benjaminwand/3d-printed-labial-pipe/0.17.2.FCStd

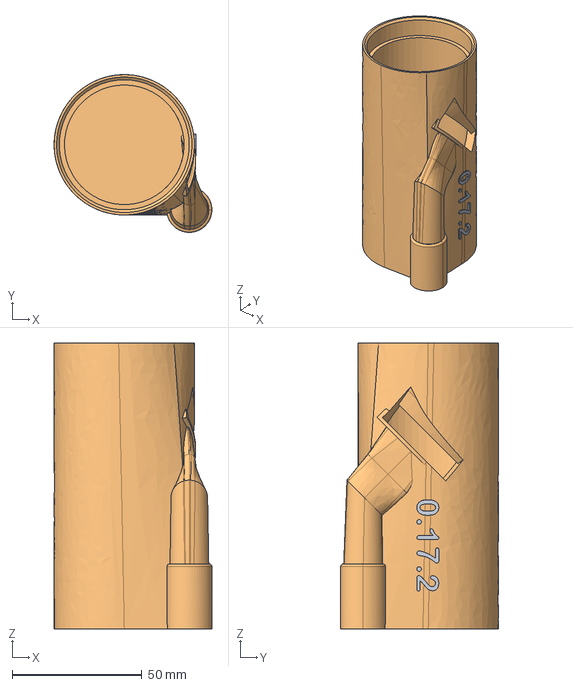
[picture p43: CAD file, 2018-04-24]
0.17.2.FCStd
60.7 x 60.7 x 110.0 mm
version number
Cut whole thing
