benjaminwand/3d-printed-labial-pipe/flue and labium only/sad+bent.FCStd

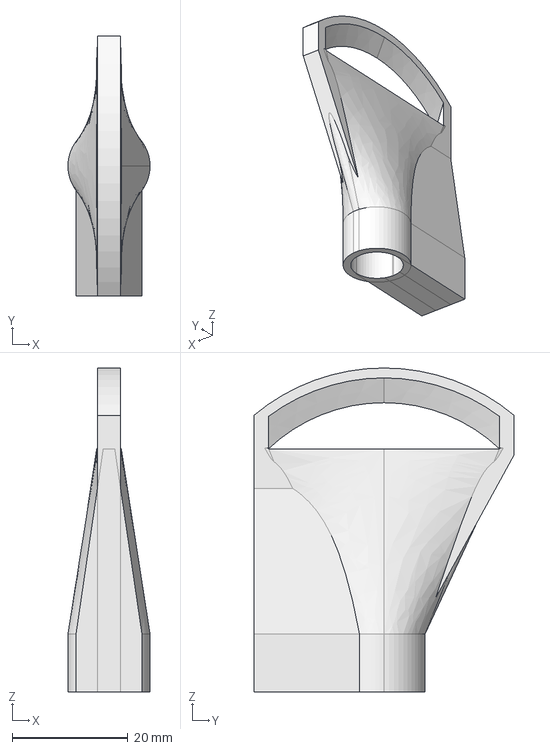
[picture p44: CAD file, 2018-07-03]
flue and labium only/sad+bent.FCStd
14.2 x 45.0 x 56.0 mm
