benjaminwand/3d-printed-labial-pipe/tuning and misc/8 tuning sliders.FCStd

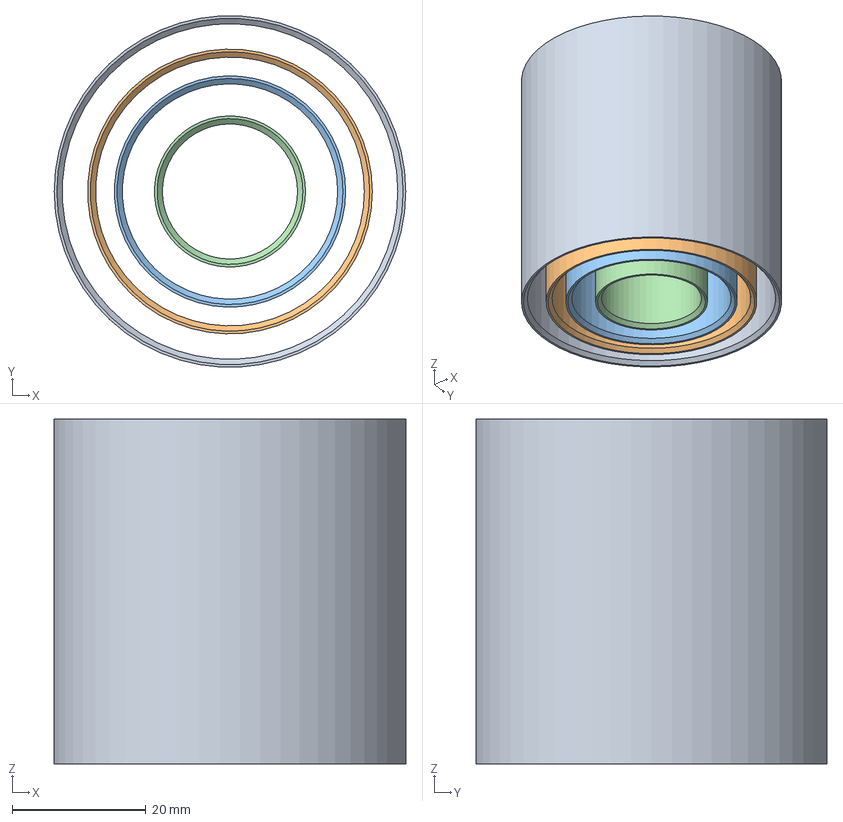
[picture p45: CAD file, 2018-03-27]
tuning and misc/8 tuning sliders.FCStd
52.6 x 52.5 x 51.6 mm
