benjaminwand/3d-printed-labial-pipe/0.15.9.FCStd

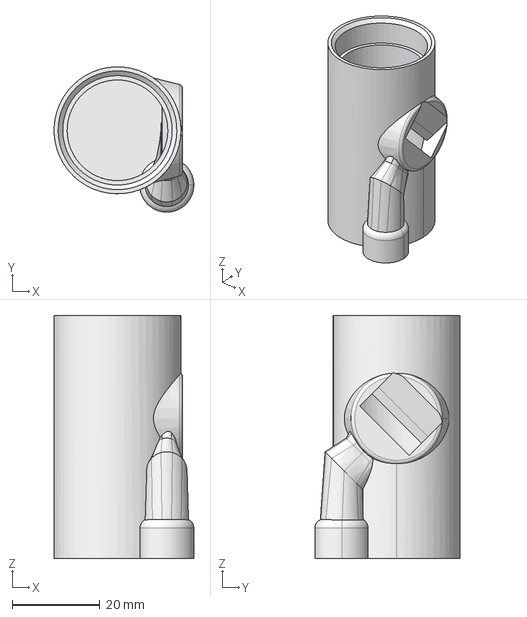
[picture p46: CAD file, 2018-04-24]
0.15.9.FCStd
31.9 x 33.2 x 55.5 mm
