benjaminwand/3d-printed-labial-pipe/flue and labium only/straight2.FCStd

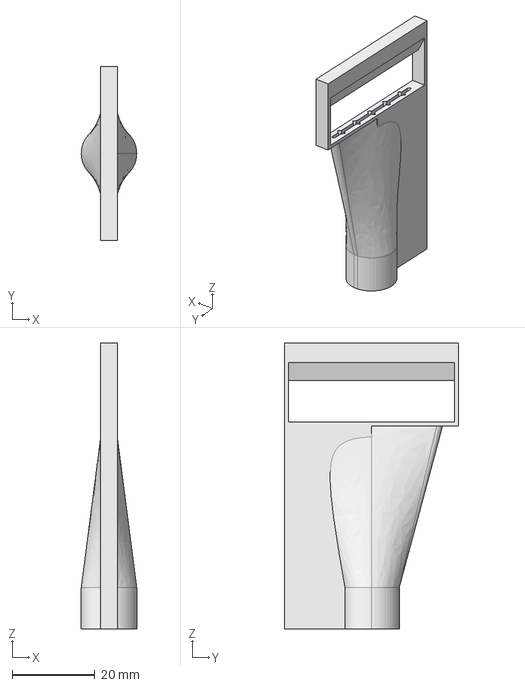
[picture p47: CAD file, 2018-05-06]
flue and labium only/straight2.FCStd
13.4 x 42.0 x 69.0 mm
