benjaminwand/3d-printed-labial-pipe/0.17.1.FCStd

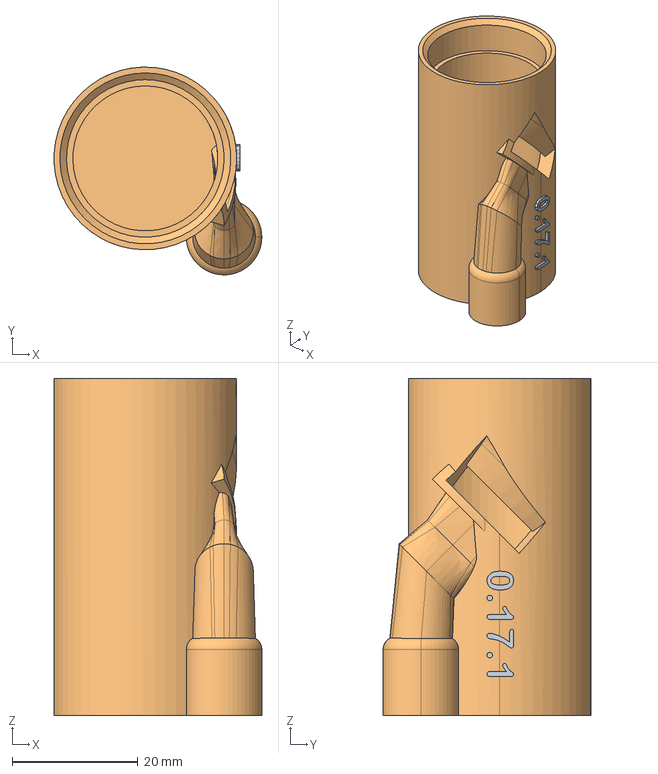
[picture p48: CAD file, 2018-04-16]
0.17.1.FCStd
33.0 x 33.0 x 53.5 mm
version number
Cut whole thing
