benjaminwand/3d-printed-labial-pipe/flue and labium only/curved-3.FCStd

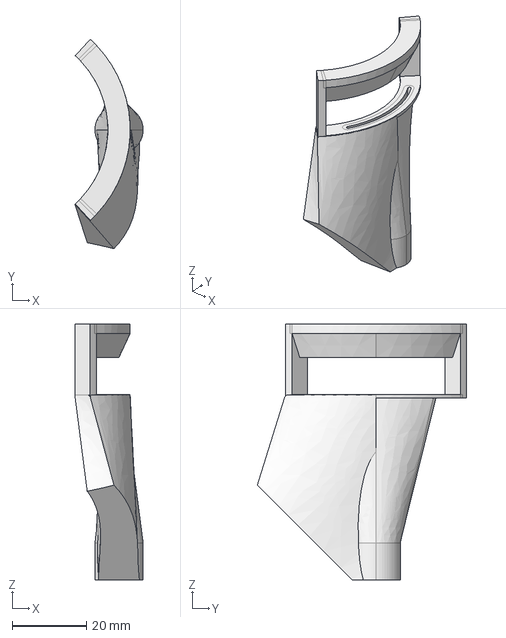
[picture p49: CAD file, 2018-04-24]
flue and labium only/curved-3.FCStd
18.4 x 56.4 x 69.0 mm
