benjaminwand/3d-printed-labial-pipe/0.17.FCStd

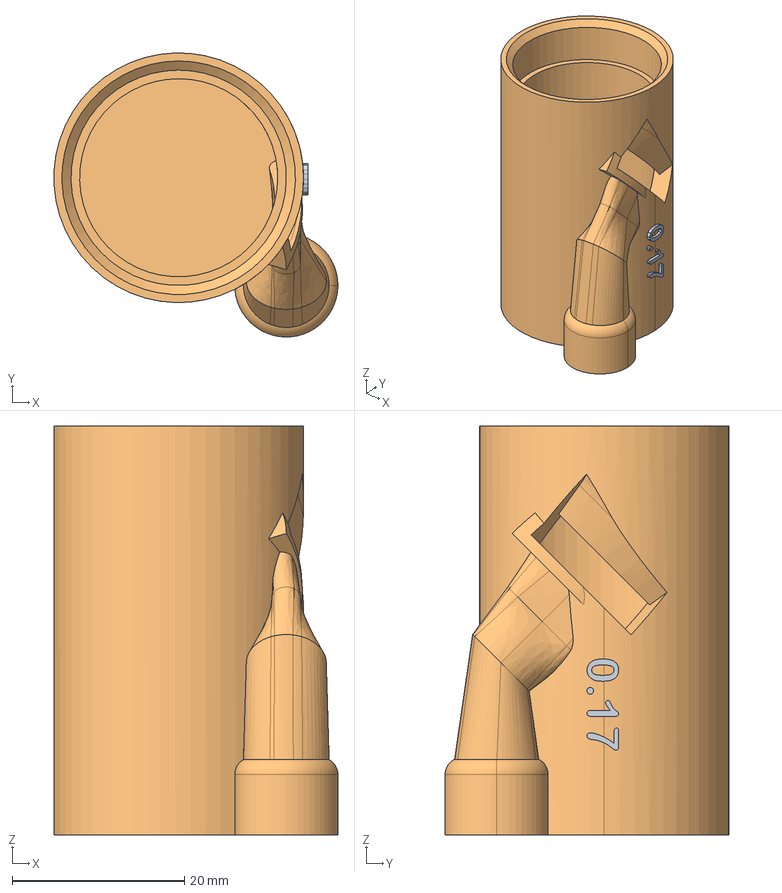
[picture p50: CAD file, 2018-04-16]
0.17.FCStd
33.0 x 33.0 x 47.5 mm
version number
Cut whole thing
