benjaminwand/3d-printed-labial-pipe/flue and labium only/curved-2.FCStd

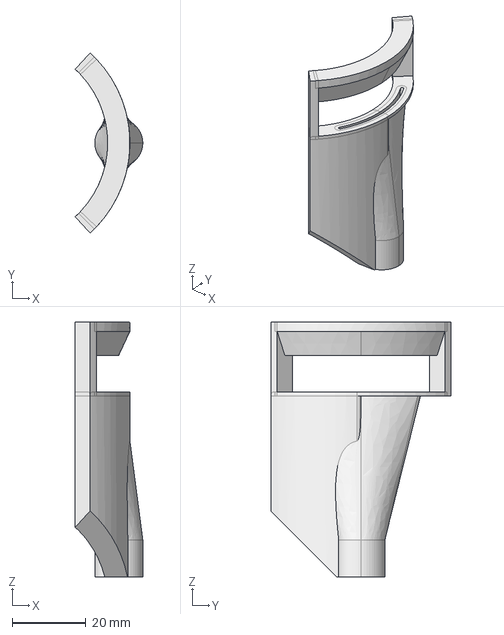
[picture p51: CAD file, 2018-04-24]
flue and labium only/curved-2.FCStd
18.3 x 48.8 x 69.0 mm
