benjaminwand/3d-printed-labial-pipe/0.08.FCStd

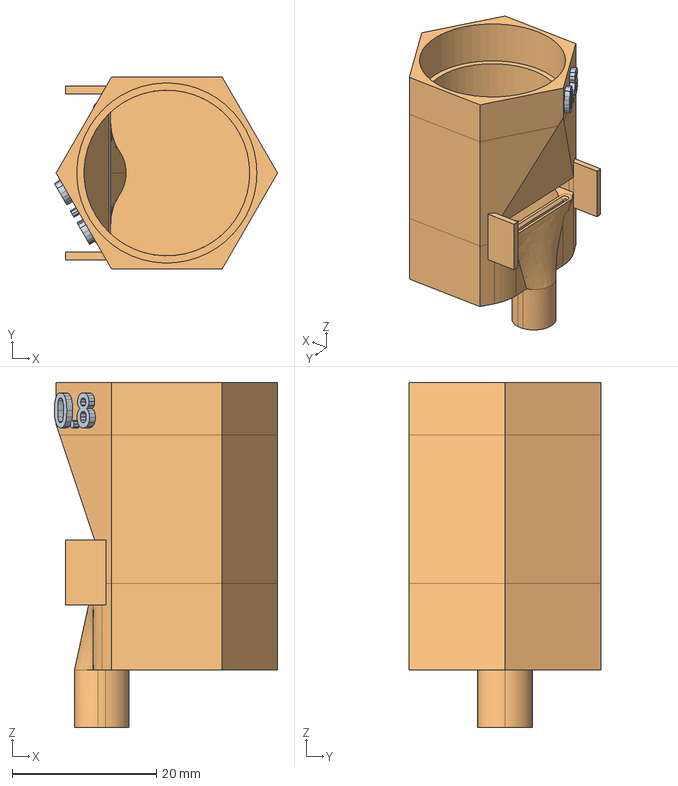
[picture p52: CAD file, 2018-04-12]
0.08.FCStd
31.0 x 26.6 x 47.9 mm
Fusion whole thing
