benjaminwand/3d-printed-labial-pipe/flue and labium only/curved.FCStd

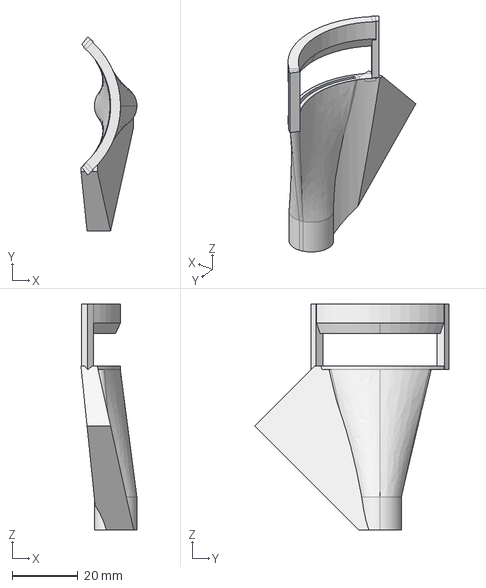
[picture p53: CAD file, 2018-04-24]
flue and labium only/curved.FCStd
17.1 x 59.3 x 69.0 mm
