benjaminwand/3d-printed-labial-pipe/flue and labium only/straight.FCStd

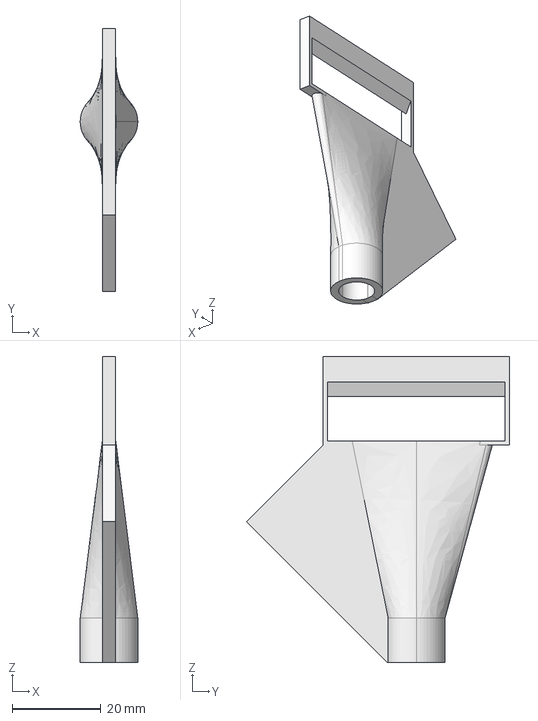
[picture p54: CAD file, 2018-04-21]
flue and labium only/straight.FCStd
13.0 x 59.2 x 69.0 mm
