benjaminwand/3d-printed-labial-pipe/0.09.1.FCStd

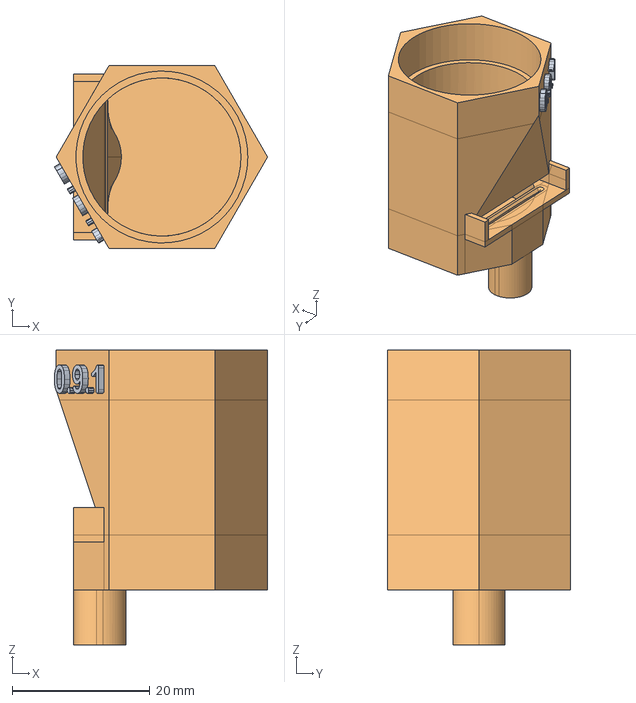
[picture p55: CAD file, 2018-04-12]
0.09.1.FCStd
31.0 x 26.6 x 42.9 mm
Fusion whole thing
