benjaminwand/3d-printed-labial-pipe/0.05.1.FCStd

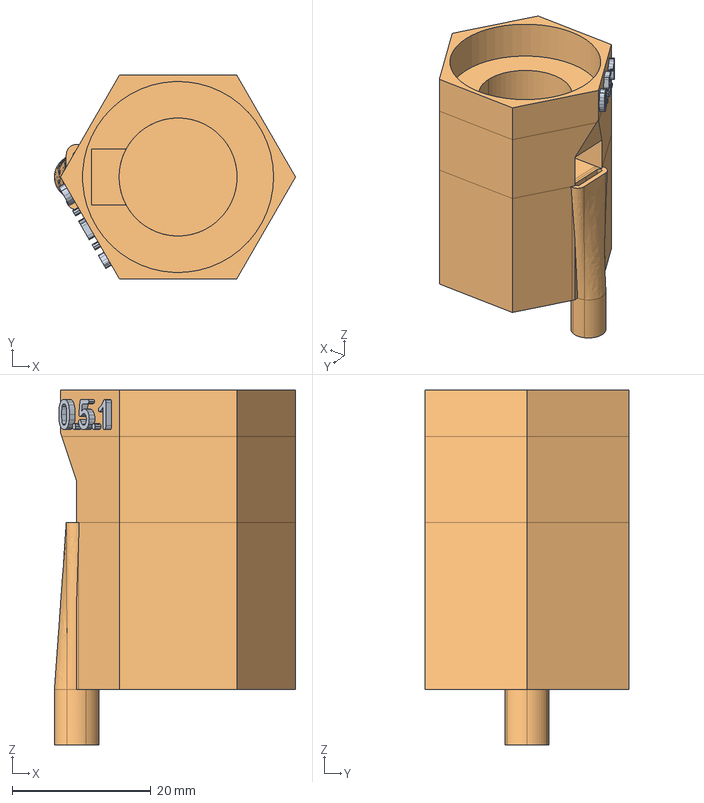
[picture p56: CAD file, 2018-04-12]
0.05.1.FCStd
34.7 x 29.3 x 51.1 mm
Fusion whole thing
