benjaminwand/3d-printed-labial-pipe/0.07.2.FCStd

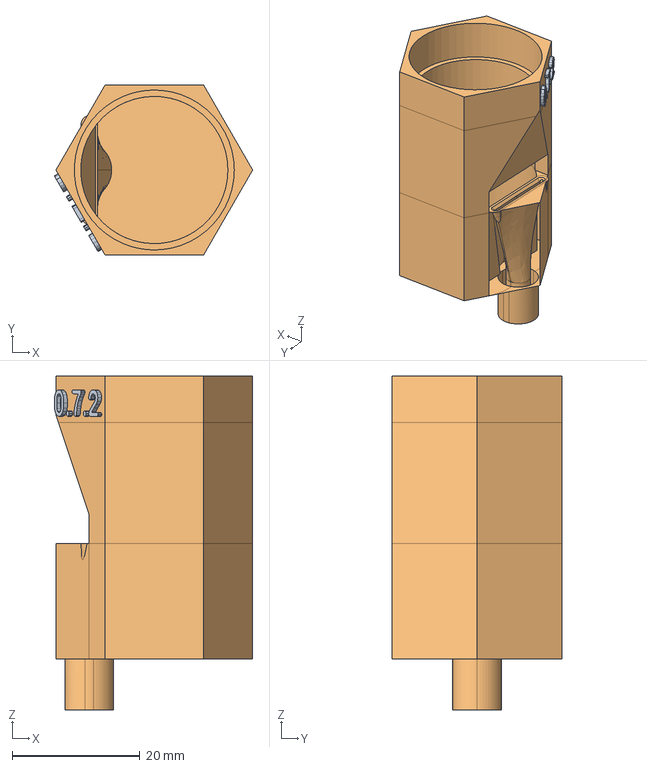
[picture p57: CAD file, 2018-04-12]
0.07.2.FCStd
31.0 x 26.6 x 52.2 mm
Fusion whole thing
