benjaminwand/3d-printed-labial-pipe/0.12.7.FCStd

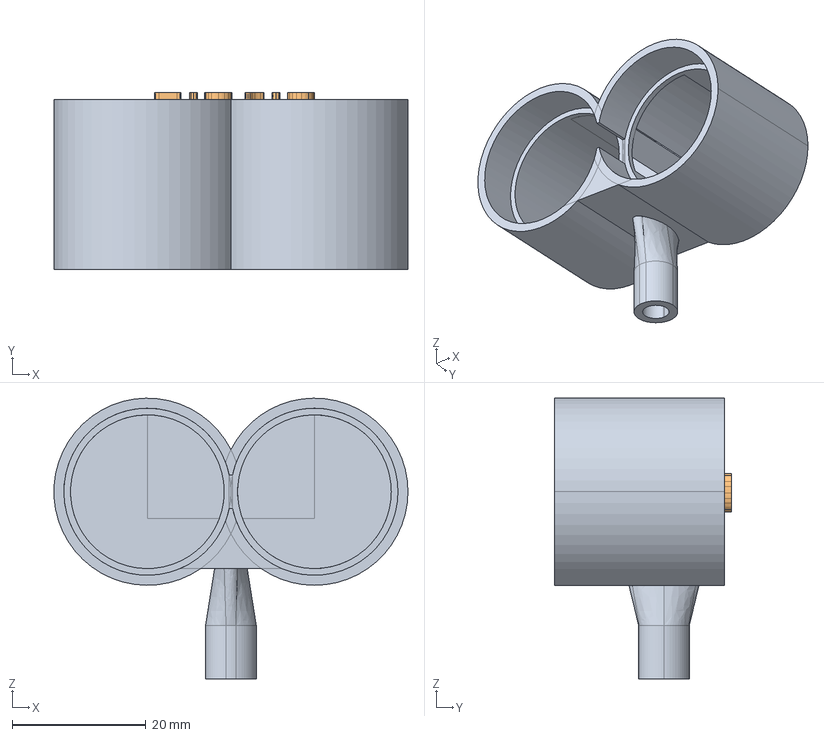
[picture p58: CAD file, 2018-04-12]
0.12.7.FCStd
53.0 x 26.4 x 42.0 mm
