benjaminwand/3d-printed-labial-pipe/0.10.5.FCStd

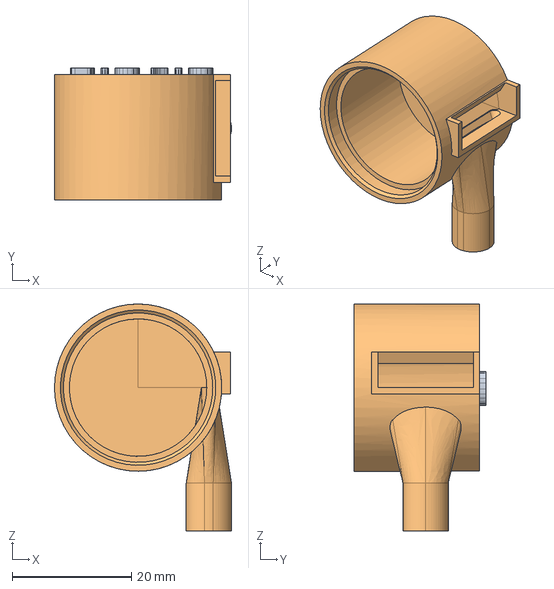
[picture p59: CAD file, 2018-04-12]
0.10.5.FCStd
29.6 x 22.0 x 38.0 mm
Cut whole thing
