benjaminwand/3d-printed-labial-pipe/0.11.5.FCStd

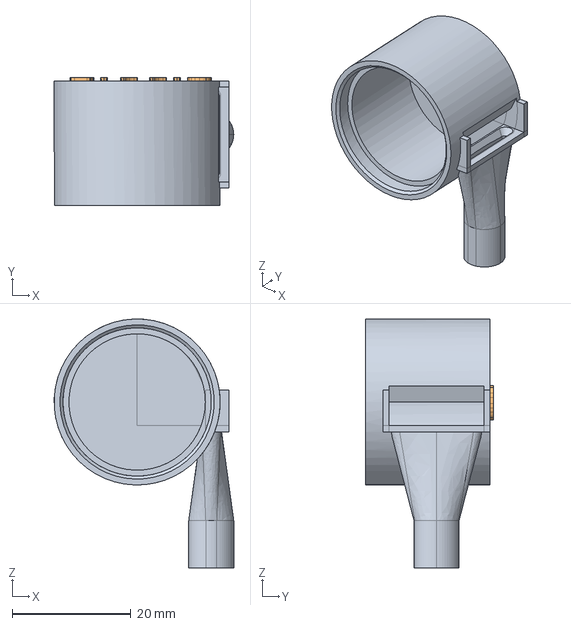
[picture p60: CAD file, 2018-04-12]
0.11.5.FCStd
30.3 x 21.5 x 42.0 mm
Cut whole thing
