benjaminwand/3d-printed-labial-pipe/0.03.3.FCStd

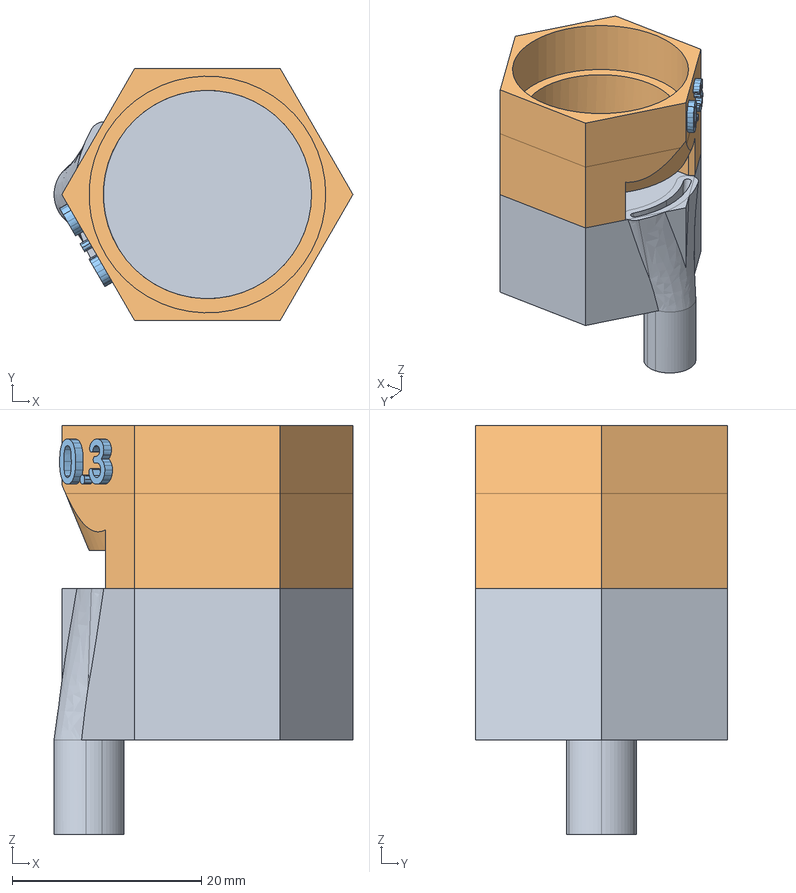
[picture p61: CAD file, 2018-04-10]
0.03.3.FCStd
31.6 x 26.6 x 43.2 mm
Cut unten
Cut oben
