benjaminwand/3d-printed-labial-pipe/0.06.FCStd

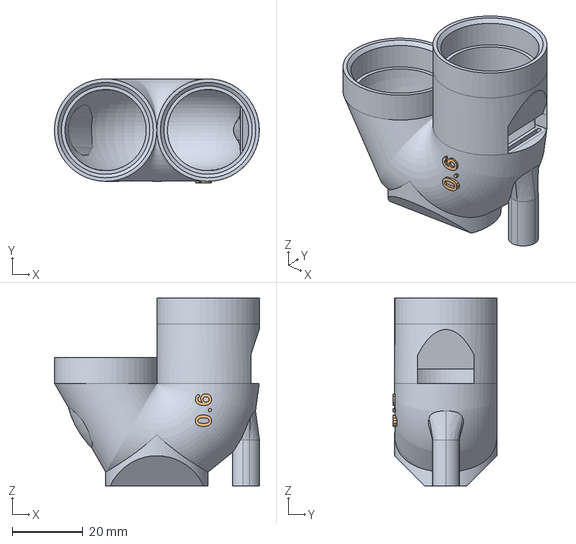
[picture p62: CAD file, 2018-04-09]
0.06.FCStd
58.0 x 29.5 x 53.1 mm
