benjaminwand/3d-printed-labial-pipe/0.03.FCStd

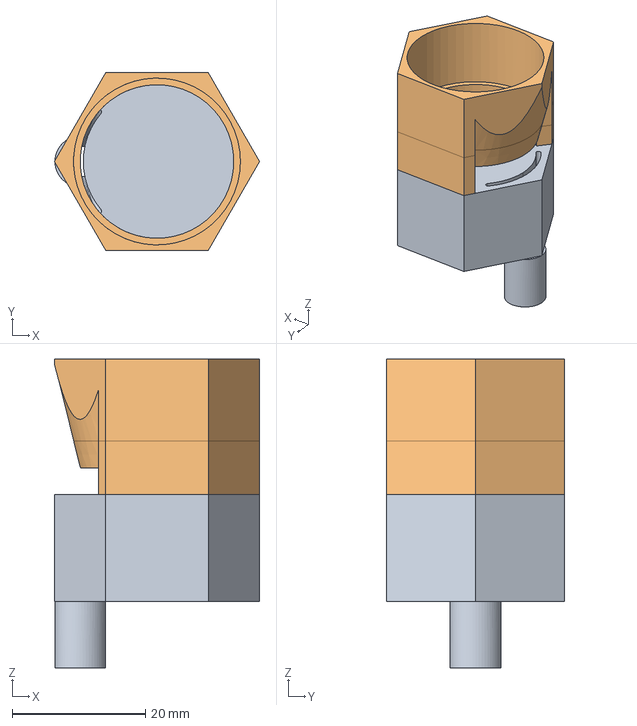
[picture p63: CAD file, 2018-04-09]
0.03.FCStd
30.8 x 26.6 x 46.3 mm
Cut Fuß
