benjaminwand/3d-printed-labial-pipe/0.07.1.FCStd

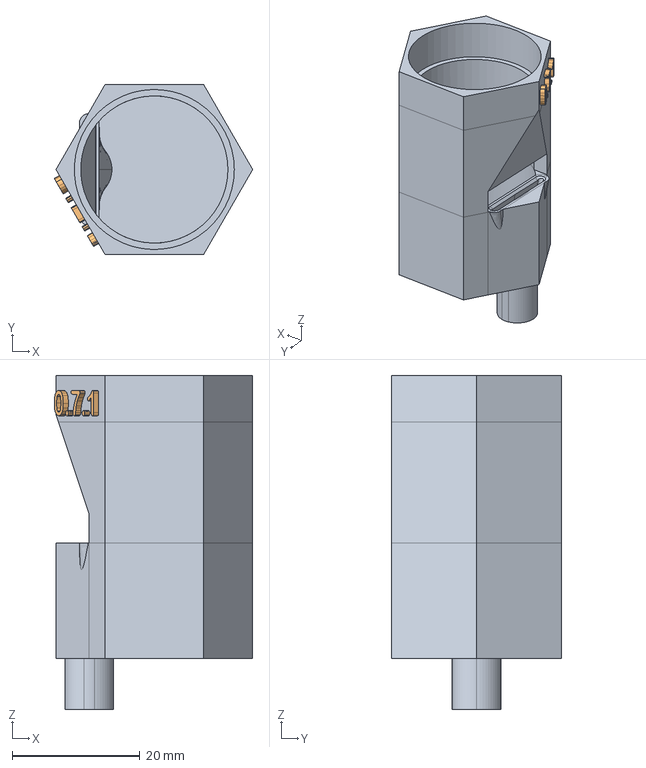
[picture p64: CAD file, 2018-04-08]
0.07.1.FCStd
31.0 x 26.6 x 52.2 mm
Fusion whiole thing
