benjaminwand/3d-printed-labial-pipe/0.15.3.FCStd

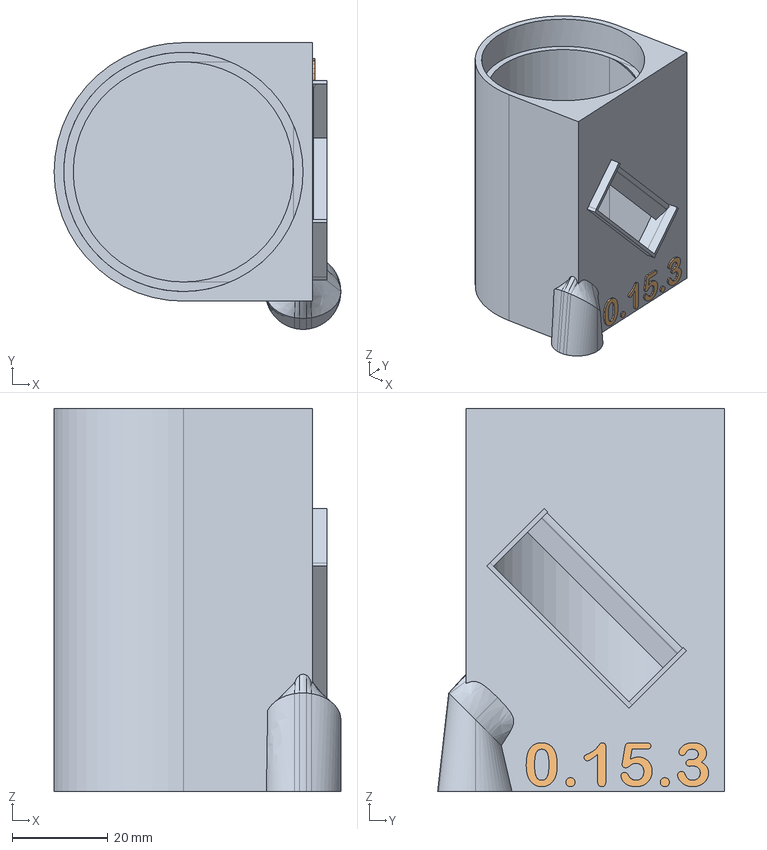
[picture p65: CAD file, 2018-04-05]
0.15.3.FCStd
59.9 x 59.9 x 80.0 mm
