benjaminwand/3d-printed-labial-pipe/0.13.FCStd

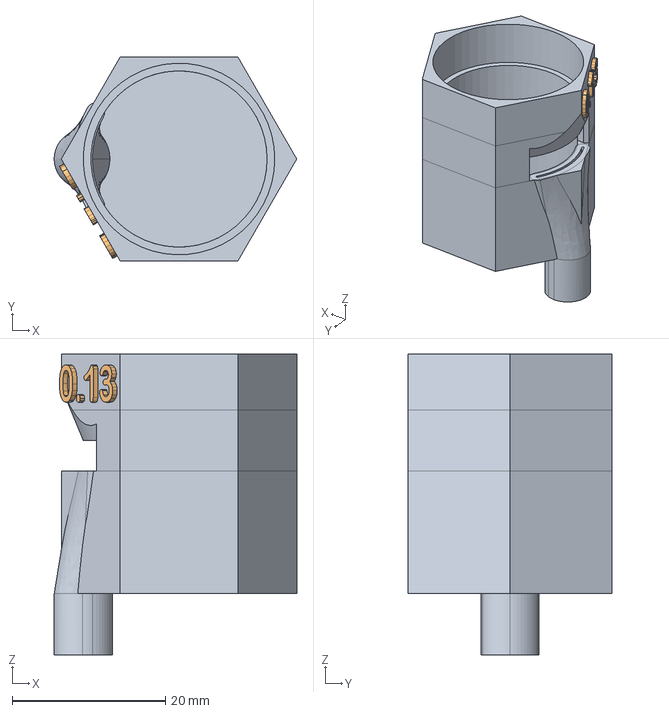
[picture p66: CAD file, 2018-04-05]
0.13.FCStd
31.7 x 26.6 x 39.3 mm
Fusion whole cut
