benjaminwand/3d-printed-labial-pipe/0.15.6.FCStd

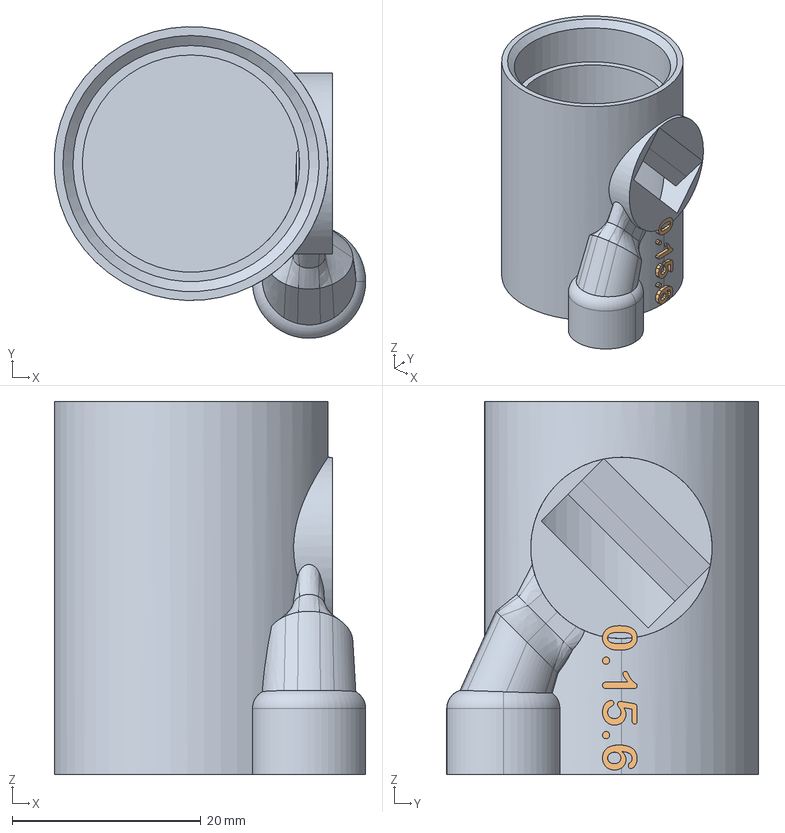
[picture p67: CAD file, 2018-04-05]
0.15.6.FCStd
33.0 x 33.0 x 39.5 mm
Cut whole thing
