benjaminwand/3d-printed-labial-pipe/0.15.1.FCStd

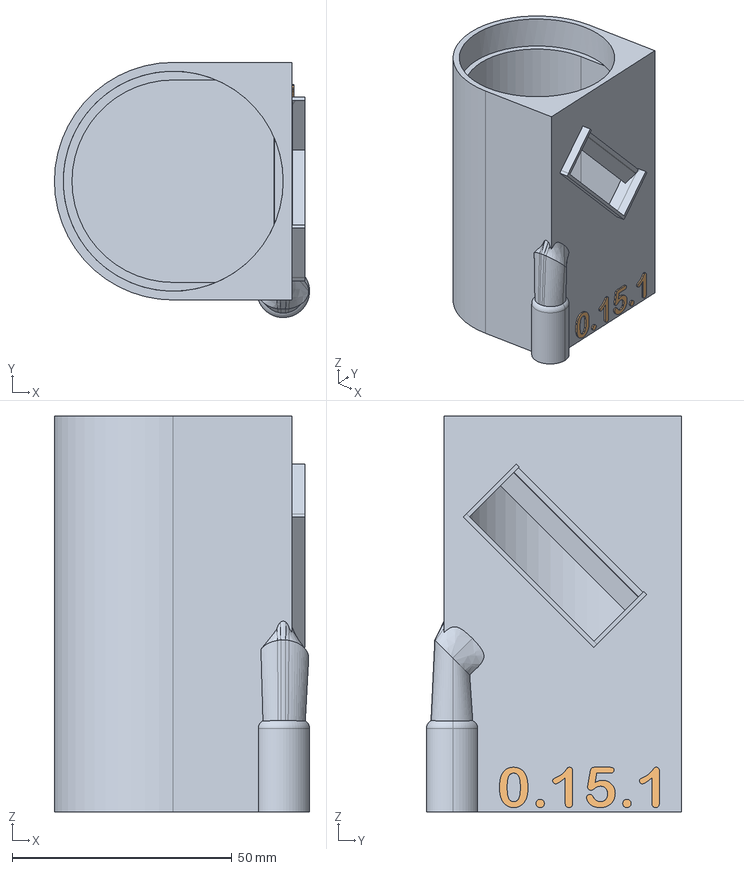
[picture p68: CAD file, 2018-04-05]
0.15.1.FCStd
58.0 x 58.0 x 90.0 mm
Cut whole thing
