benjaminwand/3d-printed-labial-pipe/0.02 proportional.FCStd

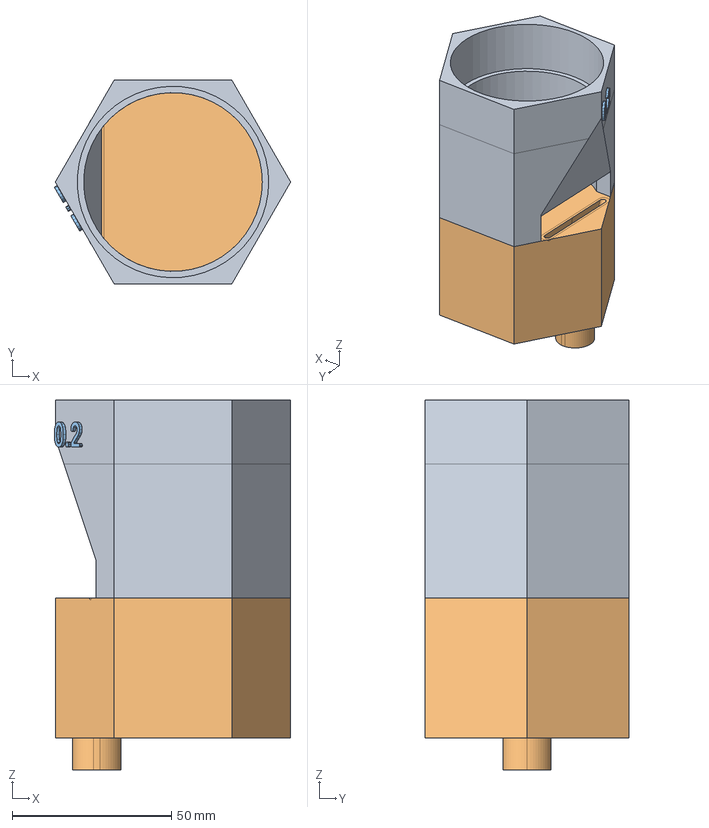
[picture p69: CAD file, 2018-04-01]
0.02 proportional.FCStd
74.1 x 63.9 x 116.0 mm
Pfeife mit Labium
