benjaminwand/3d-printed-labial-pipe/0.14.2.FCStd

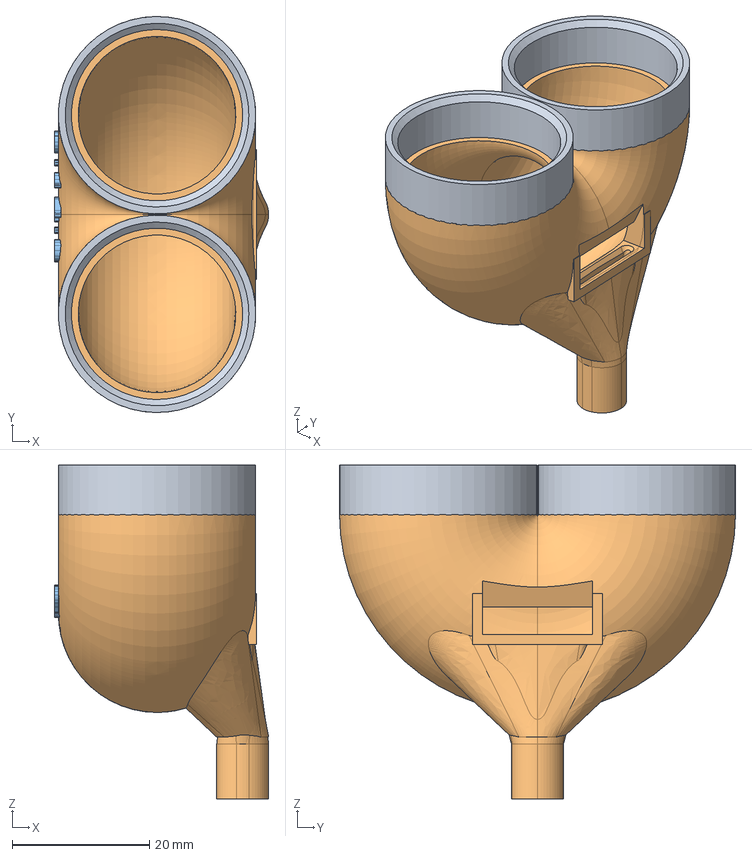
[picture p70: CAD file, 2018-04-01]
0.14.2.FCStd
31.3 x 57.8 x 48.7 mm
use both 1
use both 2
