benjaminwand/3d-printed-labial-pipe/0.15.FCStd

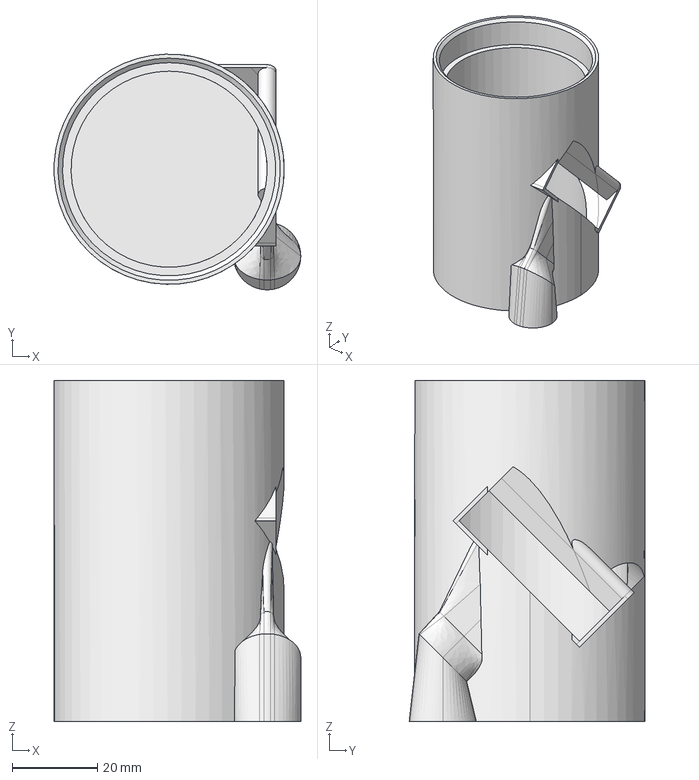
[picture p71: CAD file, 2018-04-01]
0.15.FCStd
57.9 x 55.3 x 80.0 mm
