benjaminwand/3d-printed-labial-pipe/0.15.5.FCStd

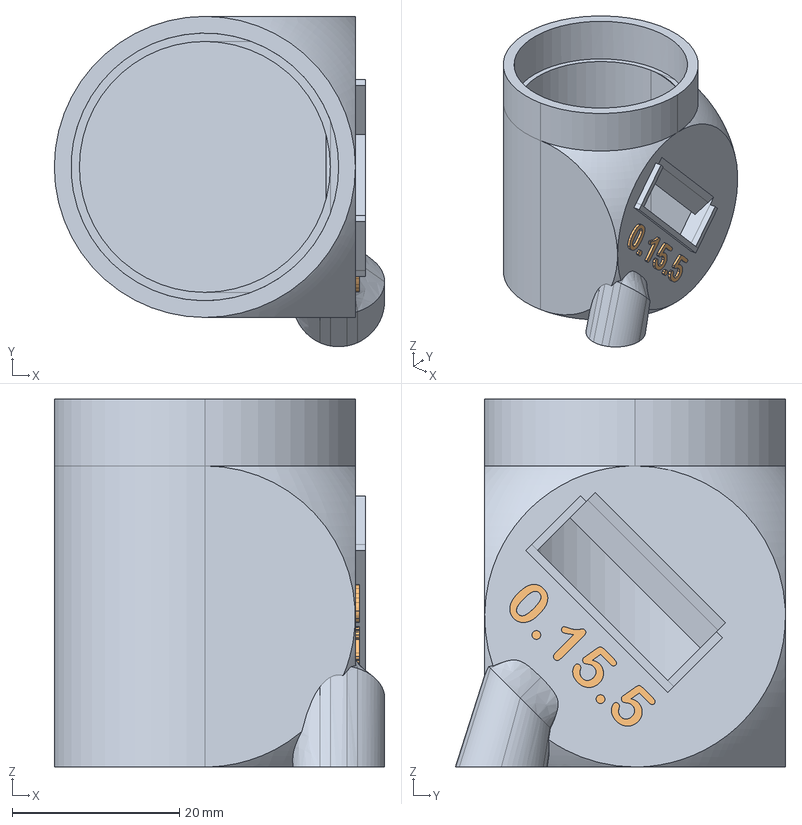
[picture p72: CAD file, 2018-04-01]
0.15.5.FCStd
39.5 x 39.5 x 44.0 mm
whole thing
