benjaminwand/3d-printed-labial-pipe/0.15.4.FCStd

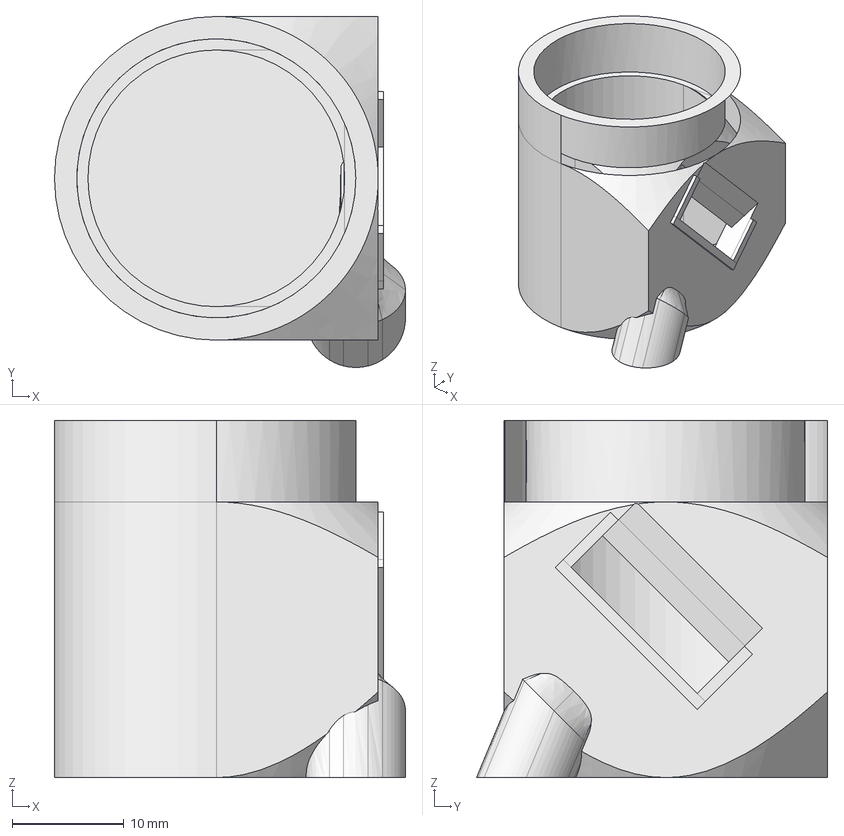
[picture p73: CAD file, 2018-03-30]
0.15.4.FCStd
31.4 x 31.4 x 32.0 mm
