benjaminwand/3d-printed-labial-pipe/0.09.FCStd

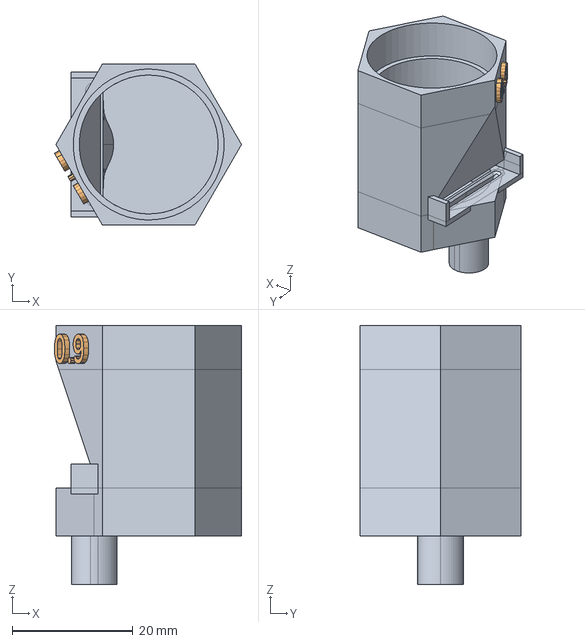
[picture p74: CAD file, 2018-03-28]
0.09.FCStd
31.0 x 26.6 x 42.9 mm
Fusion whole thing
