benjaminwand/3d-printed-labial-pipe/0.07.FCStd

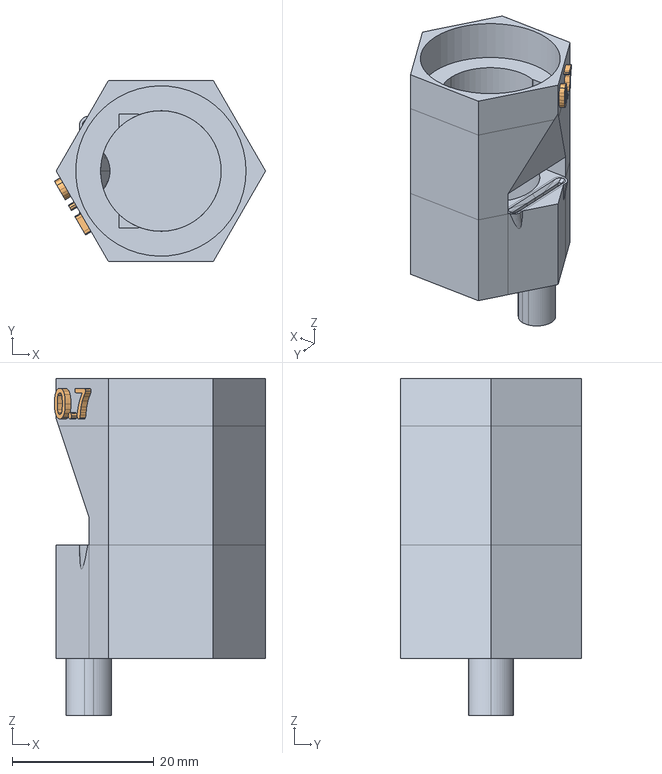
[picture p75: CAD file, 2018-03-28]
0.07.FCStd
29.8 x 25.6 x 47.5 mm
Fusion whole thing
