benjaminwand/3d-printed-labial-pipe/0.02.3.FCStd

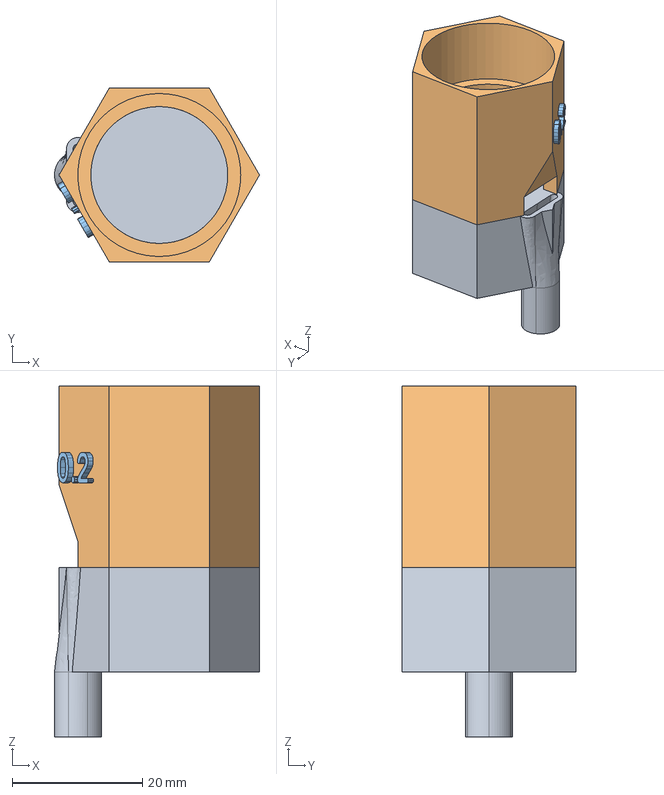
[picture p76: CAD file, 2018-03-28]
0.02.3.FCStd
31.5 x 26.6 x 53.9 mm
Cut unten
Cut oben
