benjaminwand/3d-printed-labial-pipe/0.04.2.FCStd

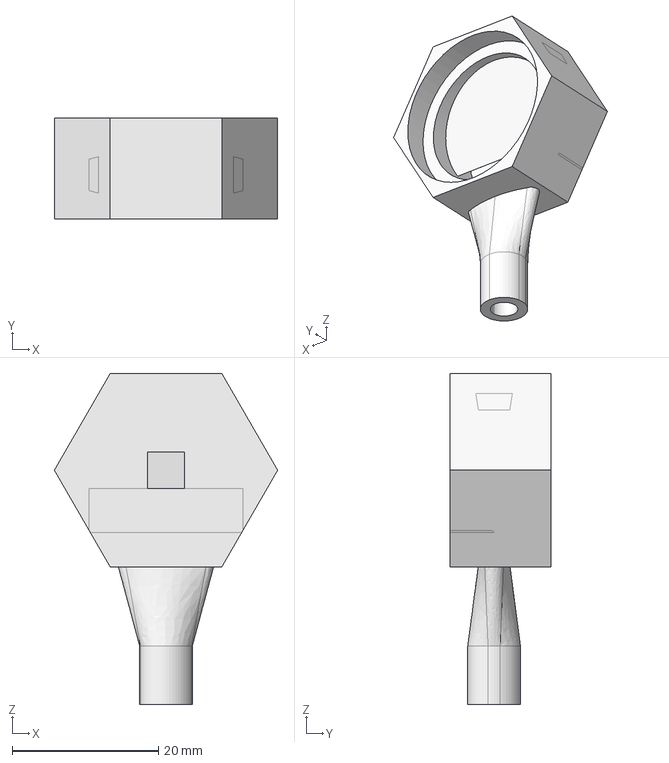
[picture p77: CAD file, 2018-03-14]
0.04.2.FCStd
30.5 x 13.8 x 45.2 mm
