benjaminwand/3d-printed-labial-pipe/0.12.6.FCStd

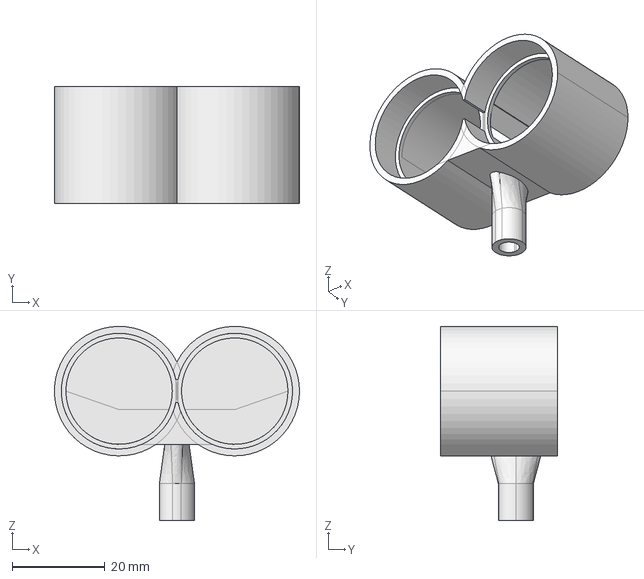
[picture p78: CAD file, 2018-03-11]
0.12.6.FCStd
53.0 x 25.4 x 42.0 mm
