benjaminwand/3d-printed-labial-pipe/0.12.5.FCStd

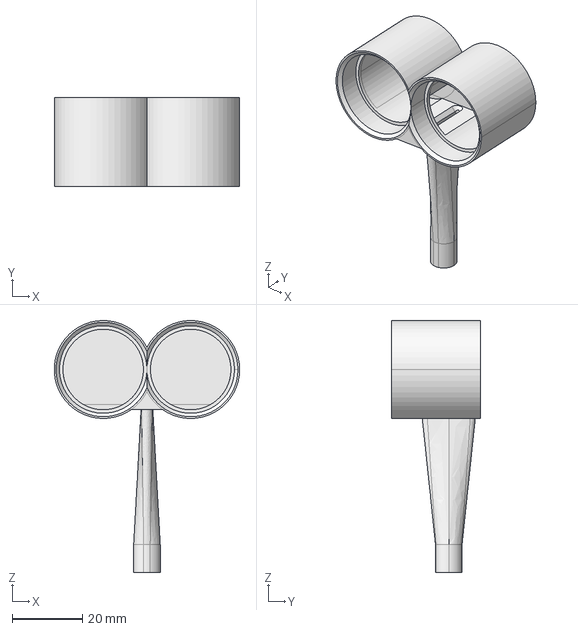
[picture p79: CAD file, 2018-03-11]
0.12.5.FCStd
53.0 x 25.4 x 72.0 mm
