benjaminwand/3d-printed-labial-pipe/0.12.4.FCStd

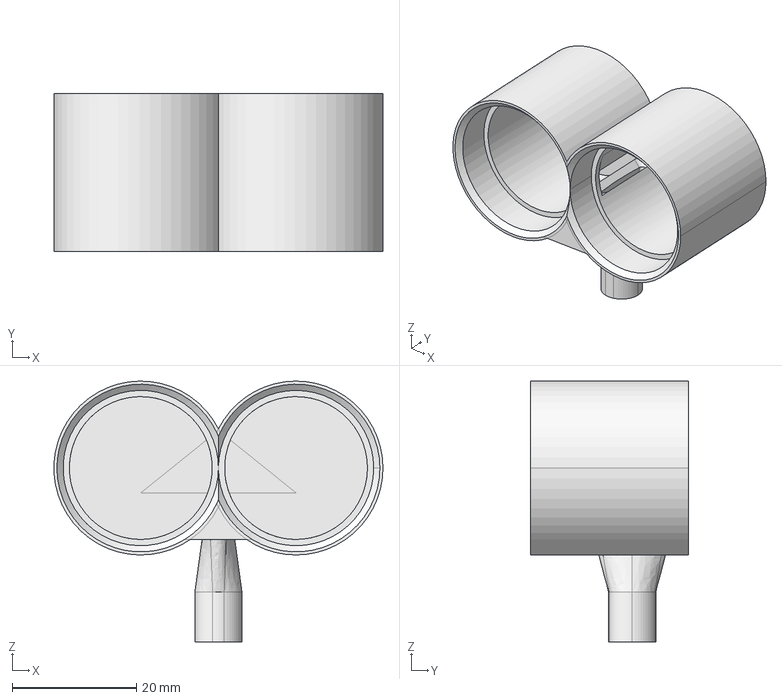
[picture p80: CAD file, 2018-03-05]
0.12.4.FCStd
53.0 x 25.4 x 42.0 mm
