benjaminwand/3d-printed-labial-pipe/0.11.4.FCStd

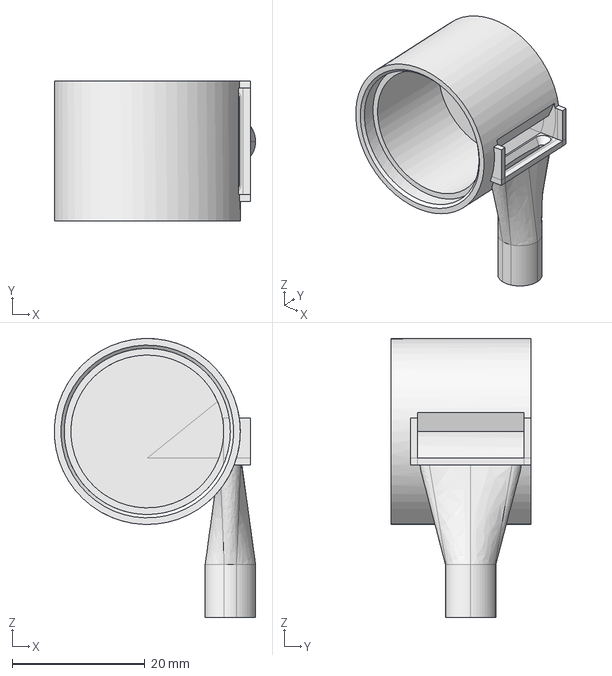
[picture p81: CAD file, 2018-03-05]
0.11.4.FCStd
30.3 x 21.0 x 42.0 mm
