benjaminwand/3d-printed-labial-pipe/0.10.4.FCStd

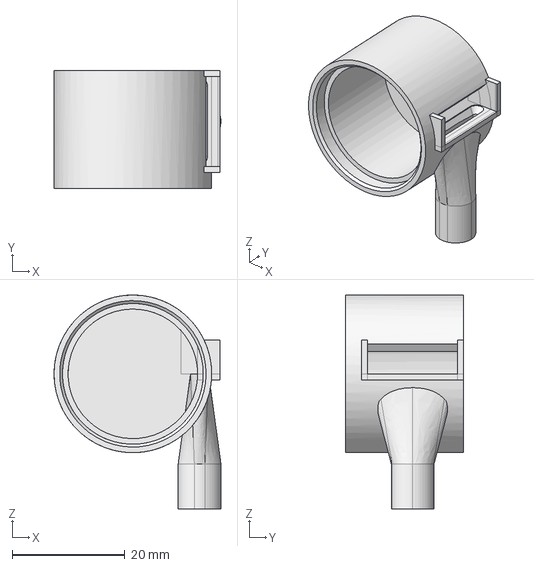
[picture p82: CAD file, 2018-03-05]
0.10.4.FCStd
29.6 x 21.0 x 38.0 mm
