benjaminwand/3d-printed-labial-pipe/0.11.FCStd

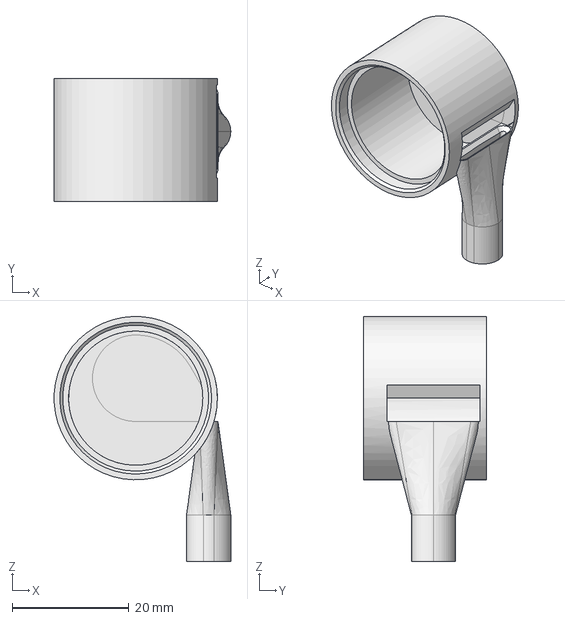
[picture p83: CAD file, 2018-03-04]
0.11.FCStd
30.3 x 21.0 x 42.0 mm
