benjaminwand/3d-printed-labial-pipe/0.10.FCStd

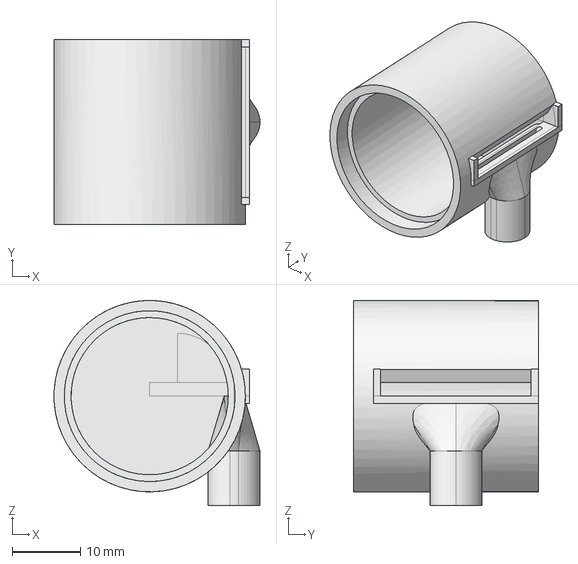
[picture p84: CAD file, 2018-03-04]
0.10.FCStd
30.1 x 27.0 x 30.0 mm
