benjaminwand/3d-printed-labial-pipe/0.12.0.FCStd

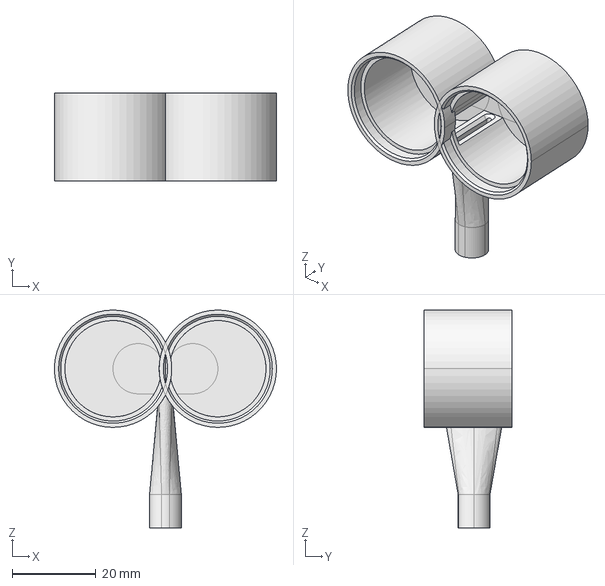
[picture p85: CAD file, 2018-03-04]
0.12.0.FCStd
53.0 x 21.0 x 52.0 mm
