benjaminwand/3d-printed-labial-pipe/0.03.1.FCStd

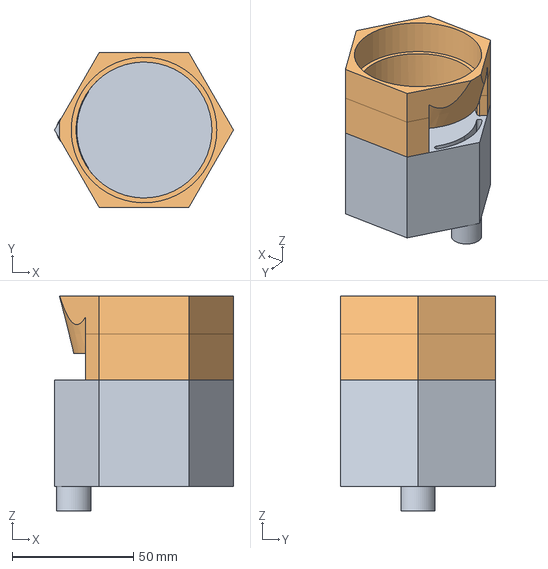
[picture p86: CAD file, 2017-11-23]
0.03.1.FCStd
73.8 x 63.9 x 88.6 mm
Cut Fuß
