benjaminwand/3d-printed-labial-pipe/0.01 sechseckig 60mm.stl

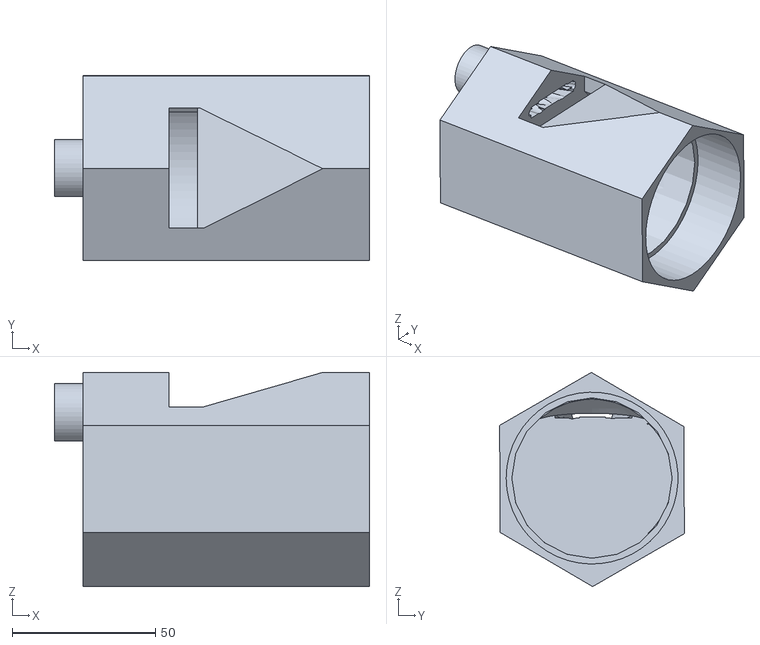
[picture p87: CAD file, 2017-10-11]
0.01 sechseckig 60mm.stl
110.0 x 64.5 x 74.8
