benjaminwand/3d-printed-labial-pipe/0.01 rund 60mm.stl

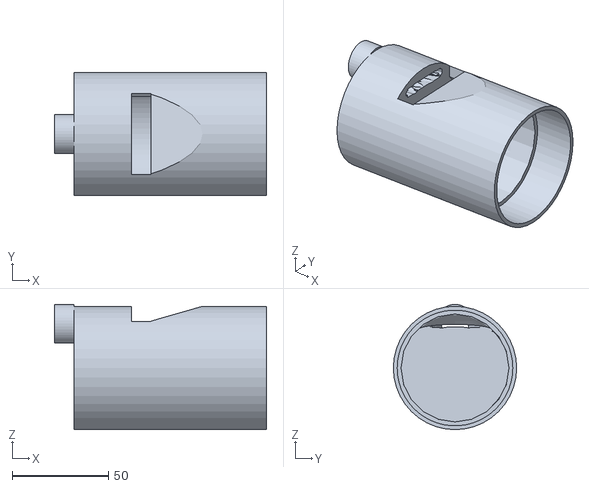
[picture p88: CAD file, 2017-10-11]
0.01 rund 60mm.stl
110.0 x 64.0 x 65.0
